Unlim8ted-Studio-Productions/unlim8ted-os/pcb/references/images/PhonefinishedV1.png

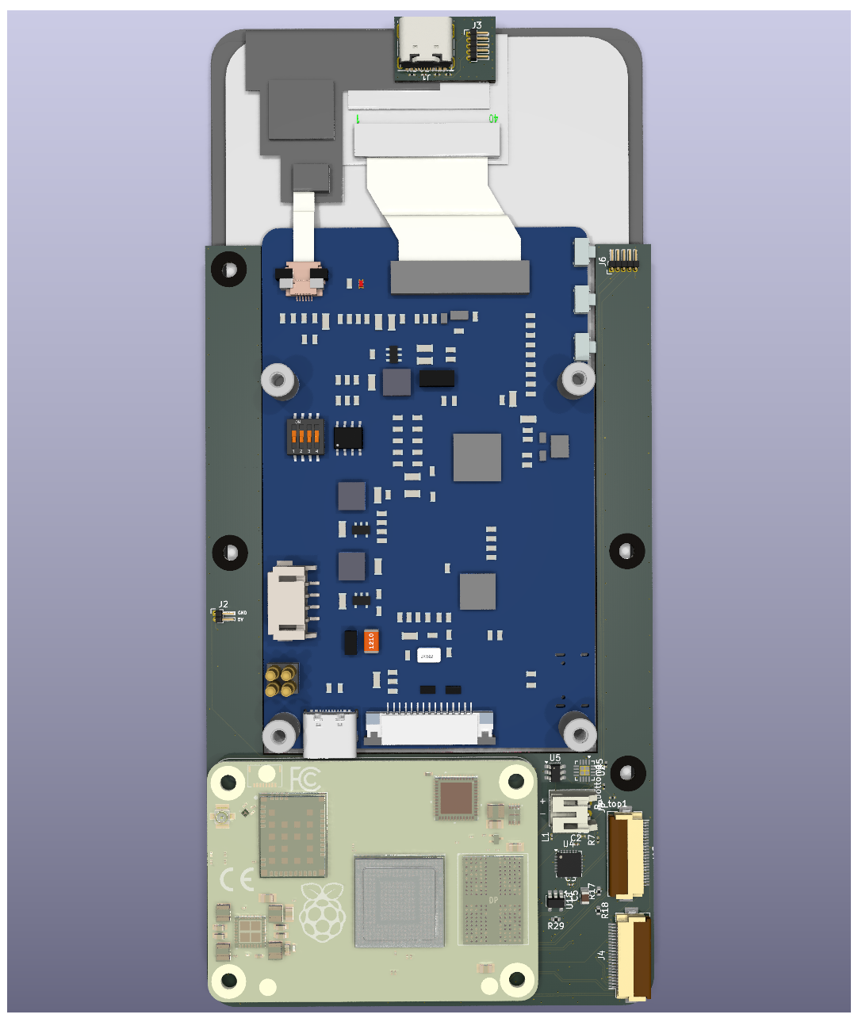
pcb/references/images/PhonefinishedV1.png
