Unlim8ted-Studio-Productions/unlim8ted-os/3d/heat_sim_cases/heat_sim_full_sfepy/meshes/battery_holder.stl

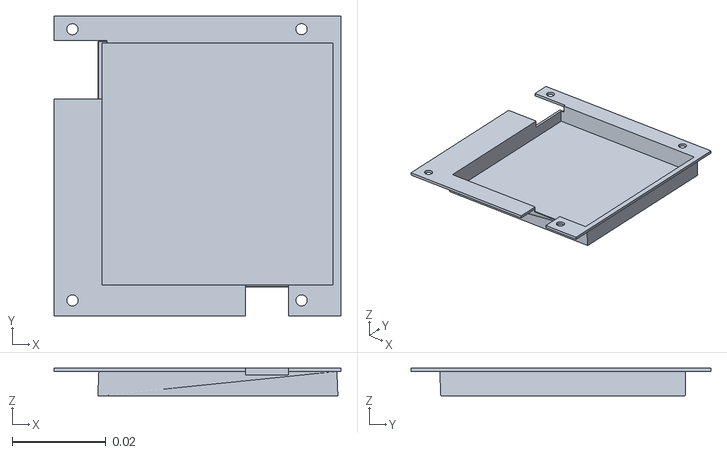
[picture p24: CAD file, 2026-06-02]
3d/heat_sim_cases/heat_sim_full_sfepy/meshes/battery_holder.stl
0.0613 x 0.0642 x 0.00593
