Unlim8ted-Studio-Productions/unlim8ted-os/3d/STL/Battery_Controller_Holder.stl

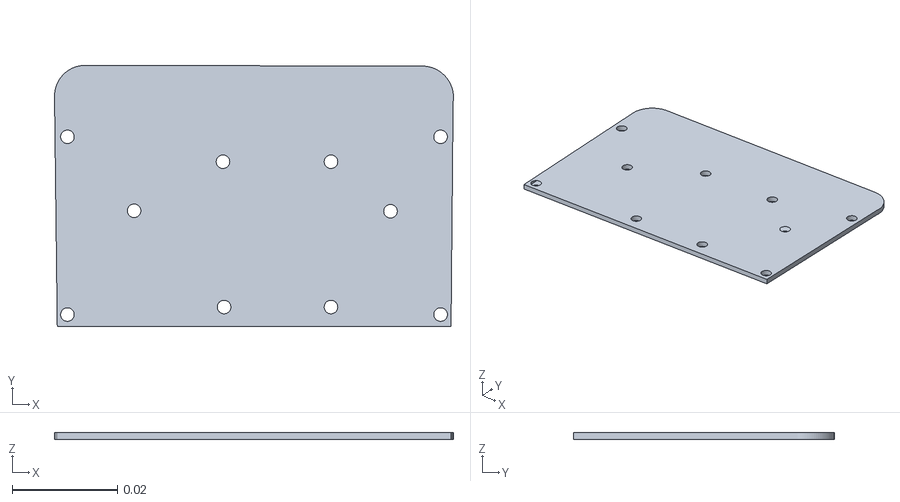
[picture p25: CAD file, 2026-05-31]
3d/STL/Battery_Controller_Holder.stl
0.0758 x 0.0496 x 0.00125
