Unlim8ted-Studio-Productions/unlim8ted-os/pcb/models/components/Arducam IMX219 Autofocus v3.step

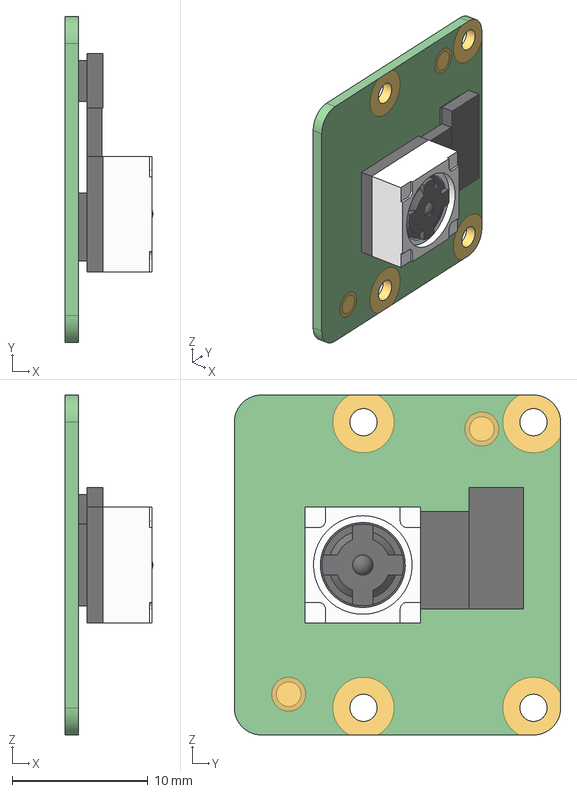
[picture p26: CAD file, 2026-04-01]
pcb/models/components/Arducam IMX219 Autofocus v3.step
6.45 x 24.0 x 25.0 mm
