Unlim8ted-Studio-Productions/unlim8ted-os/pcb/models/enclosure/phone_case.stl

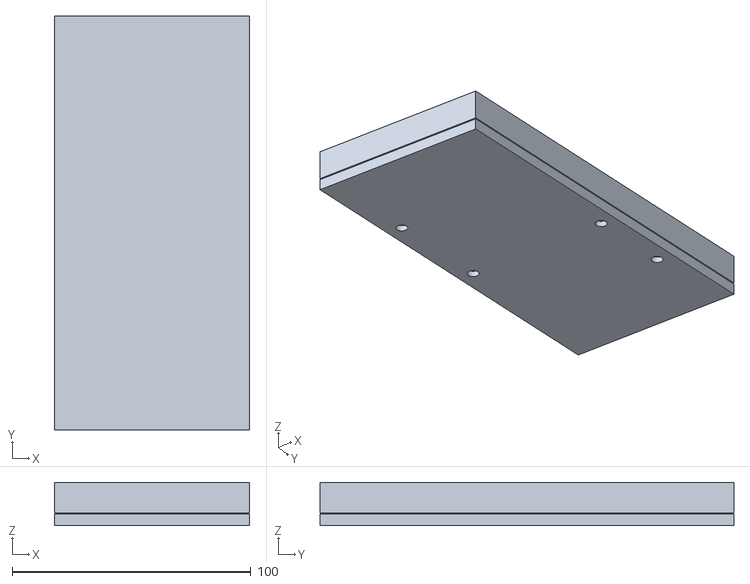
[picture p27: CAD file, 2026-04-01]
pcb/models/enclosure/phone_case.stl
81.8 x 173.5 x 18.1
