Unlim8ted-Studio-Productions/unlim8ted-os/3d/heat_sim_cases/heat_sim_full_sfepy/meshes/plane.stl

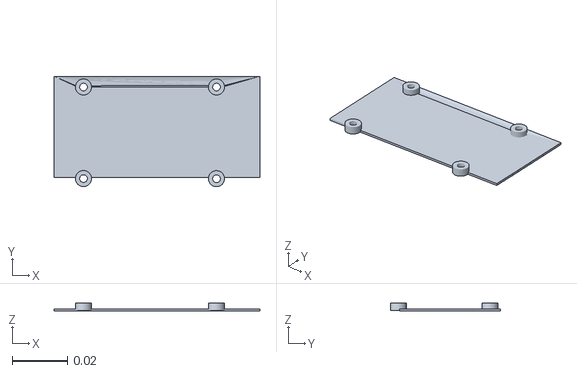
[picture p28: CAD file, 2026-06-02]
3d/heat_sim_cases/heat_sim_full_sfepy/meshes/plane.stl
0.0743 x 0.0398 x 0.00285
