Unlim8ted-Studio-Productions/unlim8ted-os/3d/STL/Back_Cover_Camera_Bump.stl

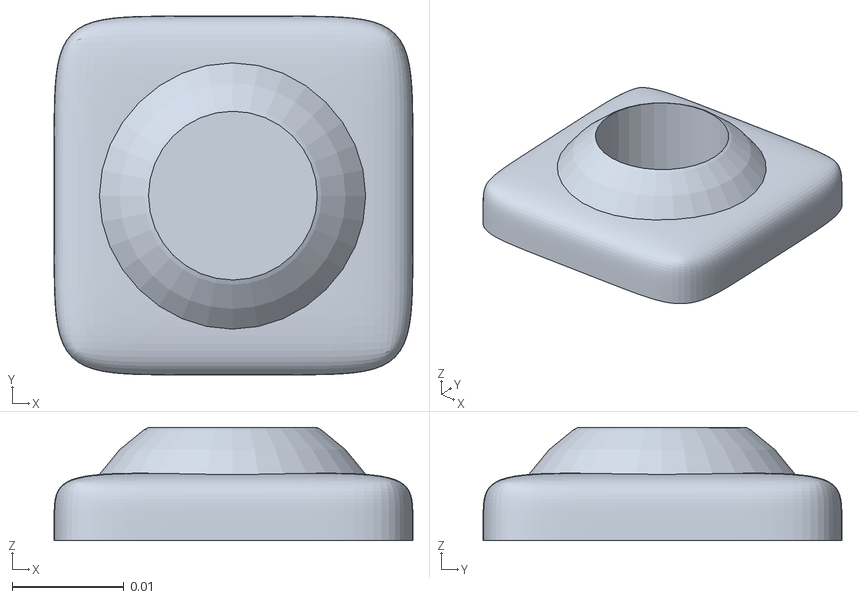
[picture p29: CAD file, 2026-05-30]
3d/STL/Back_Cover_Camera_Bump.stl
0.0322 x 0.0322 x 0.0102
