Unlim8ted-Studio-Productions/unlim8ted-os/pcb/models/enclosure/model_case51.stl

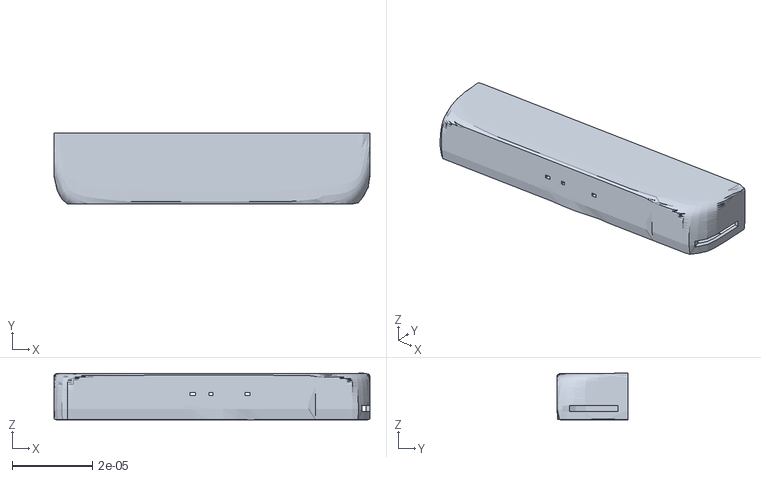
[picture p30: CAD file, 2026-04-01]
pcb/models/enclosure/model_case51.stl
7.89e-05 x 1.78e-05 x 1.17e-05
