Unlim8ted-Studio-Productions/unlim8ted-os/3d/STL/Bottom_Cover.stl

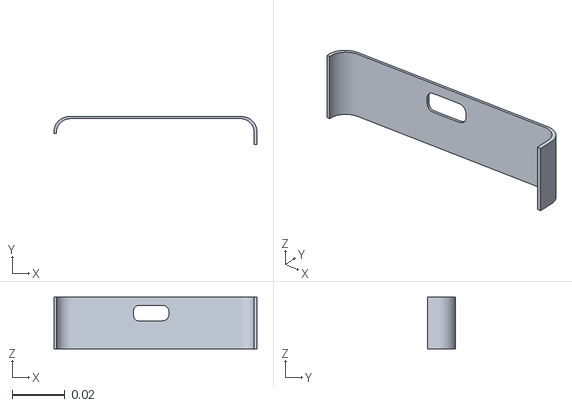
[picture p31: CAD file, 2026-05-28]
3d/STL/Bottom_Cover.stl
0.0771 x 0.0105 x 0.0196
