Unlim8ted-Studio-Productions/unlim8ted-os/pcb/models/components/Sony IMX708 v8.step

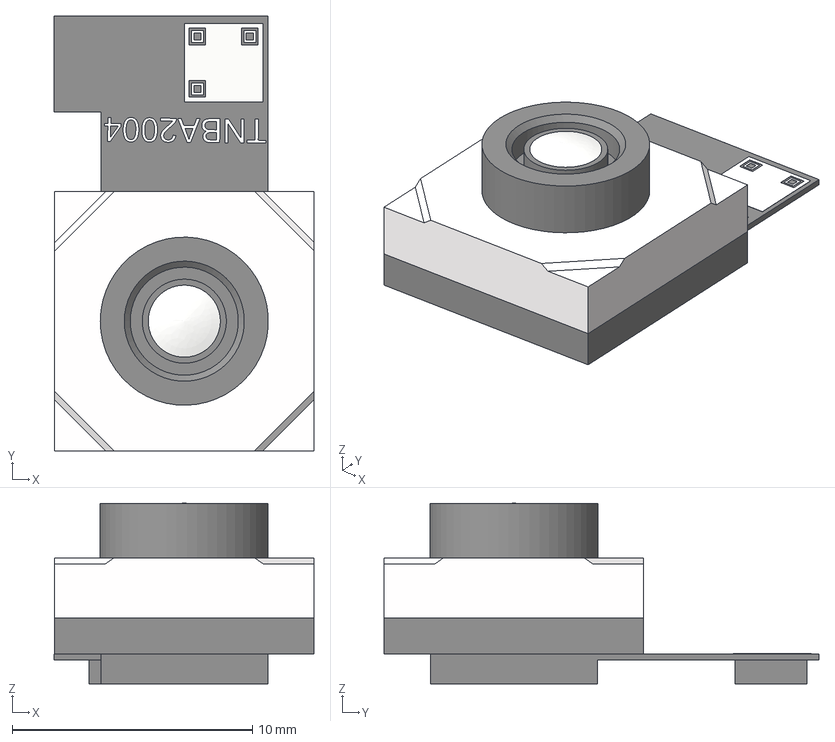
[picture p32: CAD file, 2026-04-01]
pcb/models/components/Sony IMX708 v8.step
10.8 x 18.1 x 7.53 mm
Sensor
Lens
Ring
Mount
Housing
