Unlim8ted-Studio-Productions/unlim8ted-os/pcb/models/components/IP5328P.step

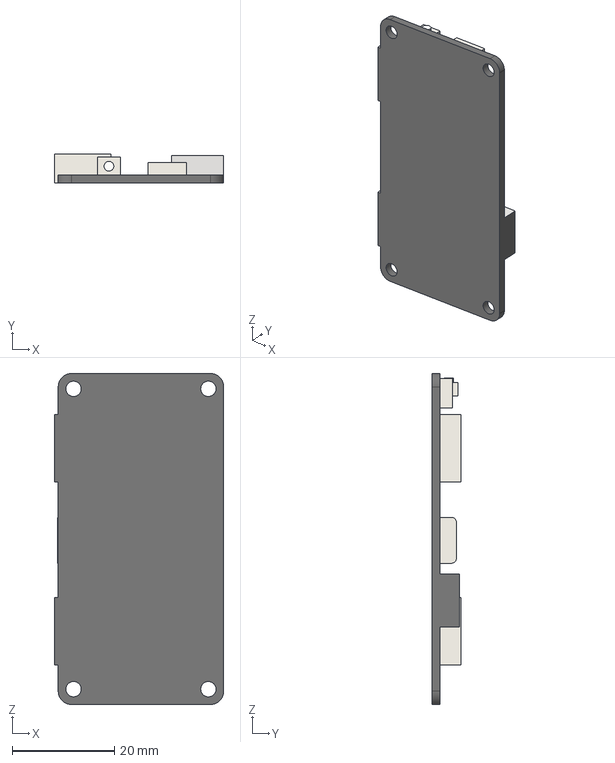
[picture p33: CAD file, 2026-04-01]
pcb/models/components/IP5328P.step
33.2 x 5.73 x 64.8 mm
