Unlim8ted-Studio-Productions/unlim8ted-os/pcb/models/components/1578 500mAh battery.step

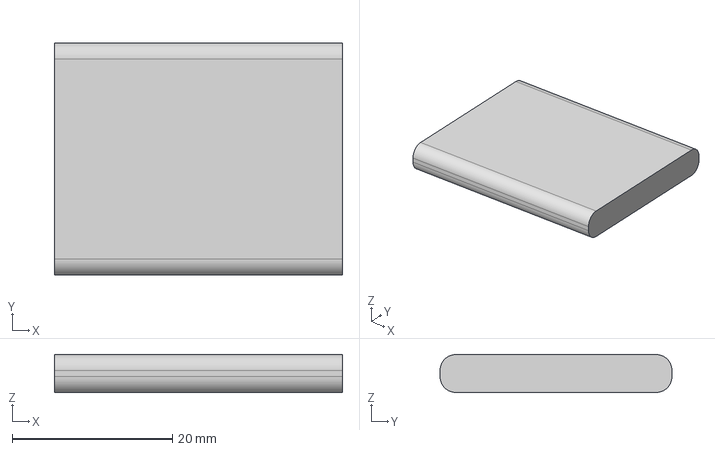
[picture p34: CAD file, 2026-04-01]
pcb/models/components/1578 500mAh battery.step
36.0 x 29.0 x 4.75 mm
