Unlim8ted-Studio-Productions/unlim8ted-os/3d/heat_sim_cases/heat_sim_full_sfepy/meshes/display_power_gnd.stl

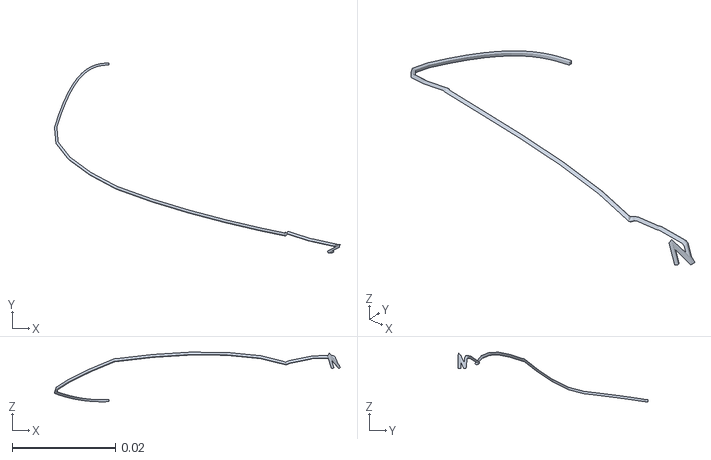
[picture p35: CAD file, 2026-06-02]
3d/heat_sim_cases/heat_sim_full_sfepy/meshes/display_power_gnd.stl
0.0554 x 0.0368 x 0.00961
