Unlim8ted-Studio-Productions/unlim8ted-os/pcb/models/components/Camera Moudule 3 v8.step

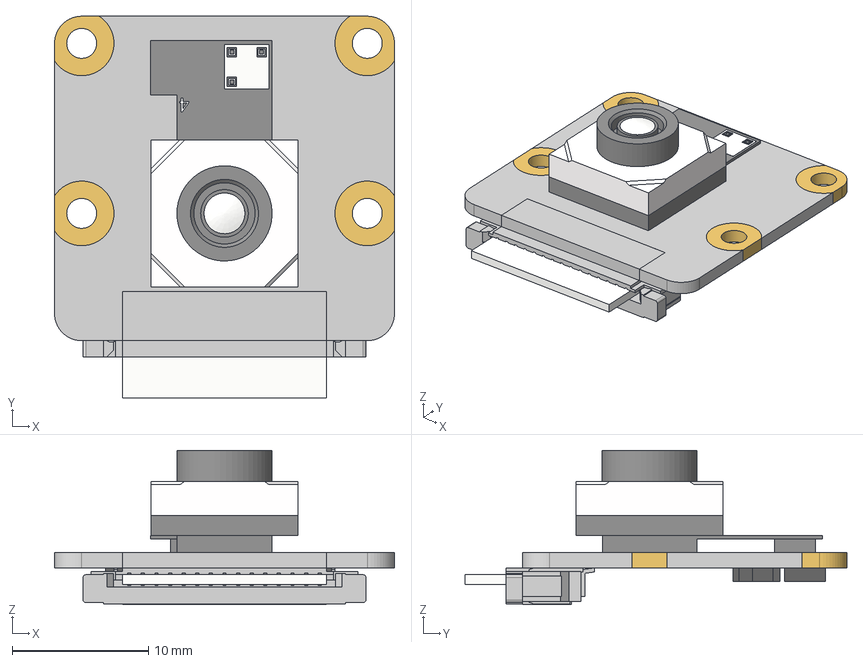
[picture p36: CAD file, 2026-04-01]
pcb/models/components/Camera Moudule 3 v8.step
25.0 x 28.1 x 11.3 mm
Board
sfw15r3ste1lf
Sensor
Lens
Ring
Mount
Housing
