Unlim8ted-Studio-Productions/unlim8ted-os/3d/heat_sim_cases/heat_sim_full_sfepy/meshes/baseboard.stl

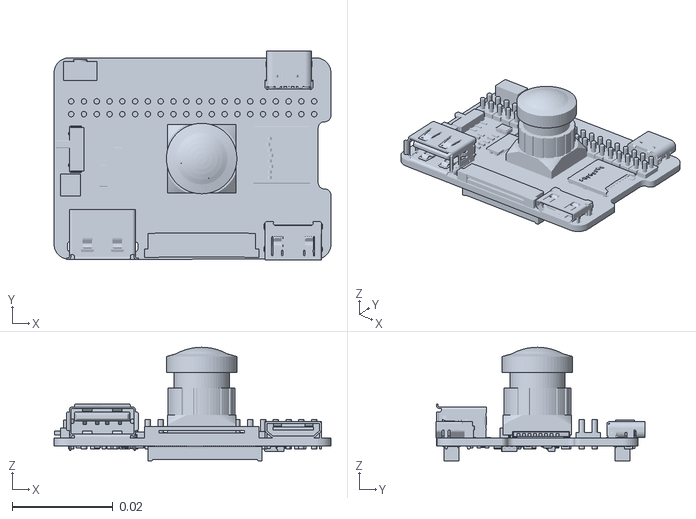
[picture p37: CAD file, 2026-06-02]
3d/heat_sim_cases/heat_sim_full_sfepy/meshes/baseboard.stl
0.055 x 0.0415 x 0.0226
