Unlim8ted-Studio-Productions/unlim8ted-os/pcb/models/components/Litio_523450.step

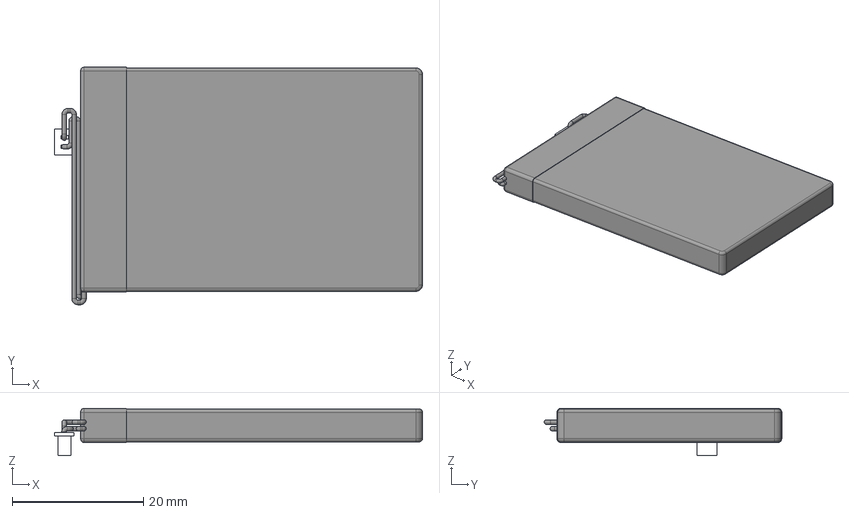
[picture p38: CAD file, 2026-04-01]
pcb/models/components/Litio_523450.step
56.0 x 36.2 x 7.20 mm
Conector
