Unlim8ted-Studio-Productions/unlim8ted-os/3d/heat_sim_cases/heat_sim_full_sfepy/meshes/typea_c_power_only_cable.stl

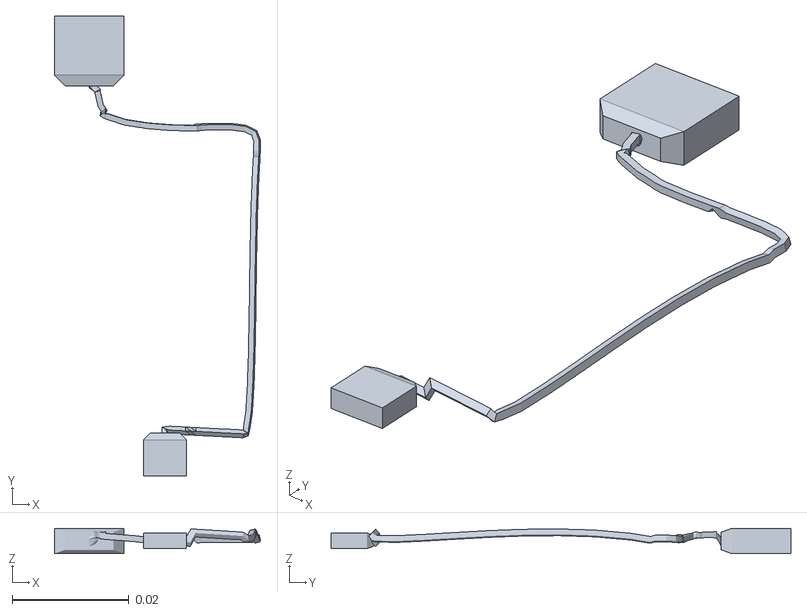
[picture p39: CAD file, 2026-06-02]
3d/heat_sim_cases/heat_sim_full_sfepy/meshes/typea_c_power_only_cable.stl
0.0354 x 0.0789 x 0.00437
