Unlim8ted-Studio-Productions/unlim8ted-os/3d/heat_sim_cases/heat_sim_full_sfepy/meshes/display.stl

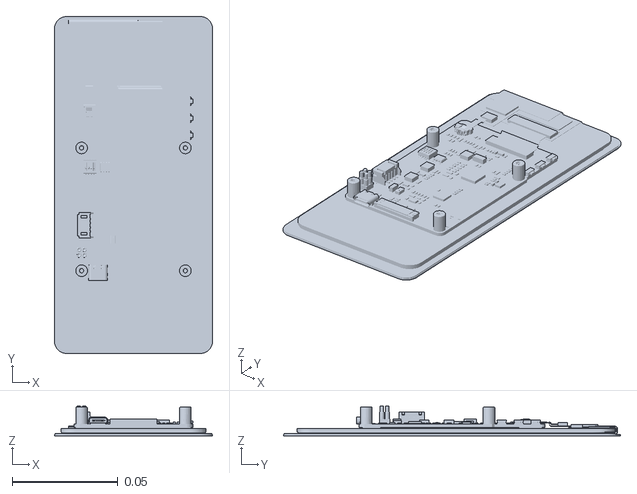
[picture p40: CAD file, 2026-06-02]
3d/heat_sim_cases/heat_sim_full_sfepy/meshes/display.stl
0.0747 x 0.159 x 0.0141
