Unlim8ted-Studio-Productions/unlim8ted-os/3d/heat_sim_cases/heat_sim_full_sfepy/meshes/battery.stl

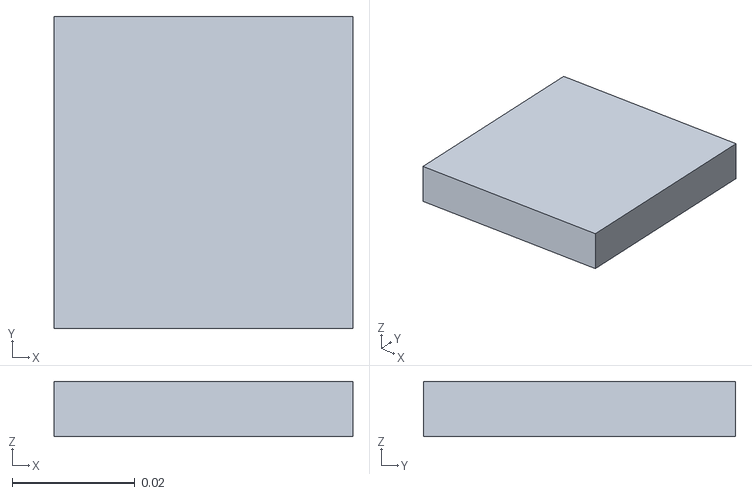
[picture p41: CAD file, 2026-06-02]
3d/heat_sim_cases/heat_sim_full_sfepy/meshes/battery.stl
0.0488 x 0.051 x 0.009
