Unlim8ted-Studio-Productions/unlim8ted-os/3d/heat_sim_cases/heat_sim_full_sfepy/meshes/jst_lipo_connector.stl

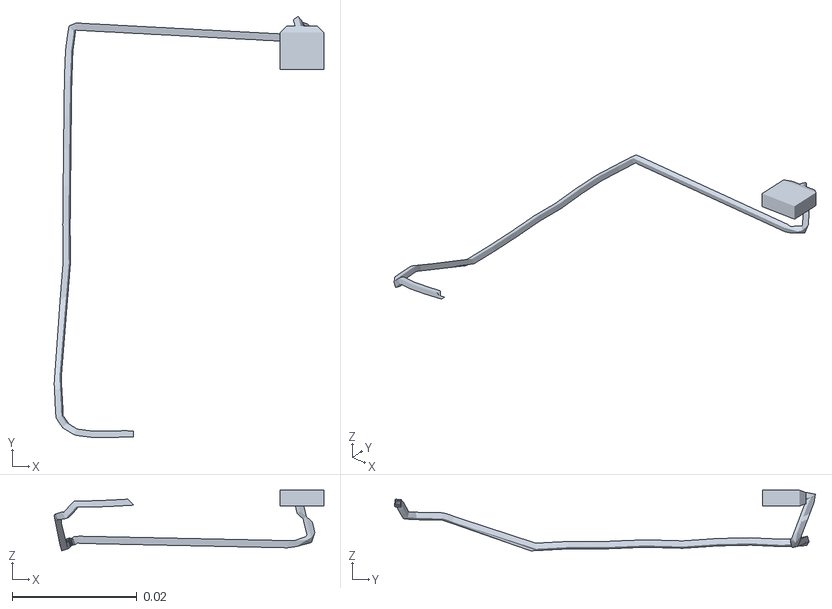
[picture p42: CAD file, 2026-06-02]
3d/heat_sim_cases/heat_sim_full_sfepy/meshes/jst_lipo_connector.stl
0.0432 x 0.0674 x 0.00974
