Unlim8ted-Studio-Productions/unlim8ted-os/3d/heat_sim_cases/heat_sim_full_sfepy/meshes/display_power_5v.stl

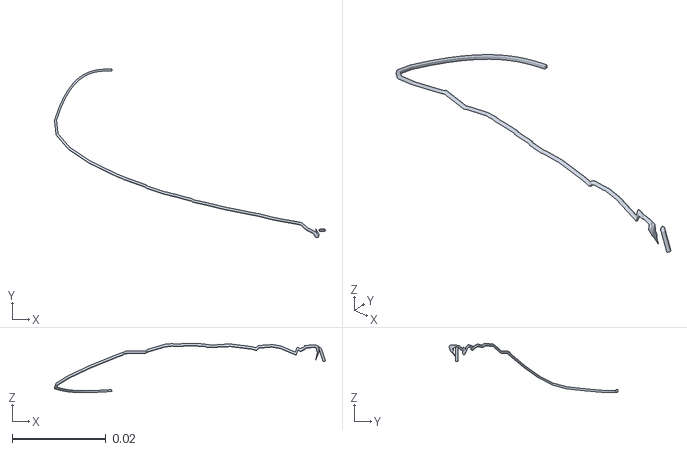
[picture p43: CAD file, 2026-06-02]
3d/heat_sim_cases/heat_sim_full_sfepy/meshes/display_power_5v.stl
0.058 x 0.0361 x 0.0106
